jgazeley/n64cartreader/firmware/rp2040/src/n64/bus/adbus.c

/**
 * @file adbus.c
 * @brief Low-level 16-bit multiplexed Address/Data bus implementation for N64 cartridges.
 */
#include "n64/pins.h"
#include "n64/bus/adbus.h"

#include "hardware/gpio.h"
#include "hardware/structs/sio.h"
#include "pico/stdlib.h"

// NOP timing constants — tuned empirically at the RP2040 default clock of 125MHz.
// Each NOP is ~8ns at 125MHz. If you overclock (e.g. 200MHz or 250MHz),
// these values will be proportionally too short and bus reads will become
// unreliable. Scale them up accordingly: new_nops = old_nops * (new_mhz / 125).
#define ADBUS_LATCH_DELAY_NOPS    7
#define ADBUS_TURNAROUND_NOPS     4
#define ADBUS_READ_ACCESS_NOPS    55
// #define ADBUS_READ_ACCESS_NOPS 120   // fallback if 55 proves unreliable
#define ADBUS_WRITE_PULSE_NOPS    25

// Mask of all four control lines in their inactive (HIGH) state.
#define ADBUS_CTRL_INACTIVE_MASK \
    ((1UL << N64_ADBUS_WR_PIN) | (1UL << N64_ADBUS_RD_PIN) | (1UL << N64_ADBUS_ALE_H_PIN) | (1UL << N64_ADBUS_ALE_L_PIN))

static bool s_adbus_is_output = false;

// --- Private Helper Functions ---
static void adbus_delay_nops(int nops) {
    for (int i = 0; i < nops; ++i) {
        __asm volatile("nop\n");
    }
}

static inline void adbus_latch_word_internal(uint16_t word, uint32_t ale_pin_mask) {
    uint32_t v = (uint32_t)word << N64_ADBUS_PIN_START;

    // Place the word on the bus.
    sio_hw->gpio_clr = N64_ADBUS_GPIO_MASK;
    sio_hw->gpio_set = v;
    adbus_delay_nops(ADBUS_LATCH_DELAY_NOPS); // Address setup time

    // Pulse the corresponding ALE line low to latch the value.
    sio_hw->gpio_clr = ale_pin_mask;
    adbus_delay_nops(ADBUS_LATCH_DELAY_NOPS); // Hold time
    // The ALE line will be de-asserted by the gpio_set(CTRL_INACTIVE_MASK)
    // at the beginning of the next bus operation.
}

//==============================================================================
// Public API Function Implementations
//==============================================================================

void adbus_set_direction(bool output) {
    if (s_adbus_is_output == output) return;  // already configured, skip

    if (output) {
        for (int i = 0; i < N64_ADBUS_PIN_COUNT; ++i) {
            uint pin = N64_ADBUS_PIN_START + i;
            gpio_set_function(pin, GPIO_FUNC_SIO);
            gpio_disable_pulls(pin);
        }
        sio_hw->gpio_oe_set = N64_ADBUS_GPIO_MASK;
        sio_hw->gpio_clr    = N64_ADBUS_GPIO_MASK;
    } else {
        for (int i = 0; i < N64_ADBUS_PIN_COUNT; ++i) {
            uint pin = N64_ADBUS_PIN_START + i;
            gpio_set_function(pin, GPIO_FUNC_SIO);
            gpio_pull_up(pin);
        }
        sio_hw->gpio_oe_clr = N64_ADBUS_GPIO_MASK;
    }

    s_adbus_is_output = output;
}


bool adbus_init(void) {
    const uint8_t control_pins[] = {
        N64_ADBUS_WR_PIN, N64_ADBUS_RD_PIN,
        N64_ADBUS_ALE_H_PIN, N64_ADBUS_ALE_L_PIN,
        N64_SYSTEM_RESET_PIN
    };

    for (size_t i = 0; i < sizeof(control_pins) / sizeof(control_pins[0]); ++i) {
        gpio_init(control_pins[i]);
        // Keep active-low controls pulled HIGH while gpio_init() leaves them as INPUT.
        // Then drive the output HIGH before switching to OUTPUT mode.
        sio_hw->gpio_set = (1u << control_pins[i]);
        gpio_pull_up(control_pins[i]);
        gpio_set_dir(control_pins[i], GPIO_OUT);
    }
    s_adbus_is_output = true;   // force adbus_set_direction to run unconditionally
    adbus_set_direction(false);
    return true;
}


void adbus_latch_address(uint32_t addr) {
    uint16_t high_word = addr >> 16;
    uint16_t low_word = (uint16_t)addr;

    // Ensure all control lines are inactive before starting the sequence.
    sio_hw->gpio_set = ADBUS_CTRL_INACTIVE_MASK;

    // 1. Drive the AD bus from the Pico.
    adbus_set_direction(true);

    // 2. Latch the high 16 bits, then the low 16 bits.
    adbus_latch_word_internal(high_word, (1UL << N64_ADBUS_ALE_H_PIN));
    adbus_latch_word_internal(low_word, (1UL << N64_ADBUS_ALE_L_PIN));

    // 3. Release the bus back to the cartridge (set to input).
    adbus_set_direction(false);
    adbus_delay_nops(ADBUS_TURNAROUND_NOPS);
}


uint16_t adbus_read_word(void) {
    // Assert /RD (drive RD_PIN LOW) to begin the read cycle.
    sio_hw->gpio_clr = (1UL << N64_ADBUS_RD_PIN);
    adbus_delay_nops(ADBUS_READ_ACCESS_NOPS);

    // Read the state of all GPIO pins at once.
    uint32_t port_val = sio_hw->gpio_in;

    // De-assert /RD (drive RD_PIN HIGH) to end the read cycle.
    sio_hw->gpio_set = (1UL << N64_ADBUS_RD_PIN);
    adbus_delay_nops(ADBUS_LATCH_DELAY_NOPS);

    // Extract and shift the 16 bits corresponding to the AD bus.
    return (uint16_t)((port_val & N64_ADBUS_GPIO_MASK) >> N64_ADBUS_PIN_START);
}

uint16_t adbus_read_word_at(uint32_t addr) {
    adbus_latch_address(addr);
    return adbus_read_word();
}


void adbus_write_word(uint16_t data) {
    adbus_set_direction(true);
    uint32_t data_bits = ((uint32_t)data << N64_ADBUS_PIN_START);
    sio_hw->gpio_clr = N64_ADBUS_GPIO_MASK;
    sio_hw->gpio_set = data_bits;
    adbus_delay_nops(ADBUS_LATCH_DELAY_NOPS);
    sio_hw->gpio_clr = (1UL << N64_ADBUS_WR_PIN);
    adbus_delay_nops(ADBUS_WRITE_PULSE_NOPS);
    sio_hw->gpio_set = (1UL << N64_ADBUS_WR_PIN);
    adbus_delay_nops(ADBUS_LATCH_DELAY_NOPS);
    adbus_set_direction(false);
}

void adbus_write_word_at(uint32_t addr, uint16_t data) {
    adbus_latch_address(addr);
    adbus_write_word(data);
}

void adbus_write_words_at(uint32_t addr, const uint16_t *data, size_t count) {
    if (!data || count == 0) {
        return;
    }

    adbus_latch_address(addr);
    for (size_t i = 0; i < count; ++i) {
        adbus_write_word(data[i]);
    }
}


void adbus_bus_warmup(void) {
    // Ensure all control lines are HIGH (inactive).
    sio_hw->gpio_set = ADBUS_CTRL_INACTIVE_MASK;
    // Release the bus to the cartridge.
    adbus_set_direction(false);
}


void adbus_assert_reset(bool active) {
    if (active) {
        gpio_put(N64_SYSTEM_RESET_PIN, 0);
        sleep_ms(20);
    } else {
        gpio_put(N64_SYSTEM_RESET_PIN, 1);
        sleep_ms(150);
    }
}
